mpinese/dac/simulations/tina-ti/I2V_stability.jpg

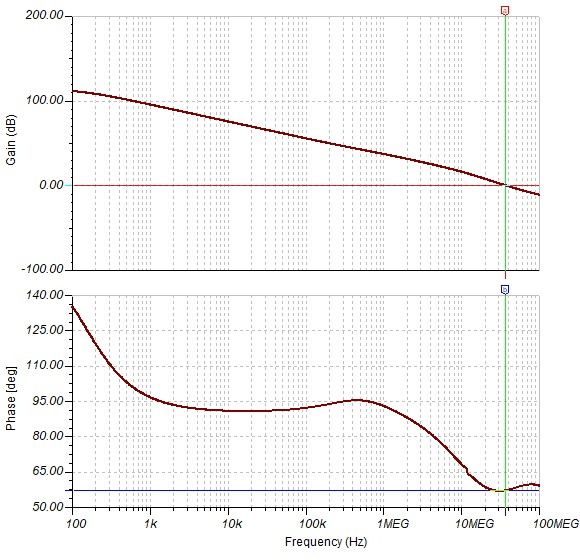
simulations/tina-ti/I2V_stability.jpg
